F4HTB/uSDX-mOnO-PA/pictures/IMG_20220408_203908.jpg

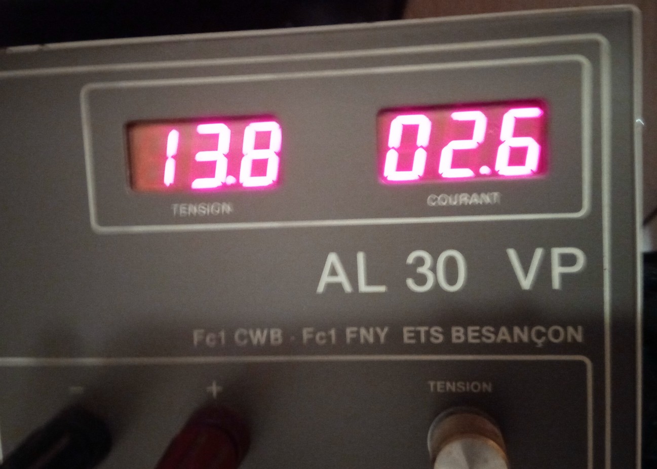
pictures/IMG_20220408_203908.jpg
