F4HTB/uSDX-mOnO-PA/Simulation/usdx_mOnO_PA_IRF530.asc

C1: cap; 10n
C2: cap; 100p
C3: cap; 200p
C4: cap; 100p
C5: cap; 12p
C6: cap; 33p
C7: cap; 10n
C8: cap; 1n
C9: cap; 100µ
C10: cap; 10n
L1: ind2; 5.76µ
L2: ind2; 13µ
L3: ind; 320n
L4: ind; 320n
L5: ind; 10µ
M1: nmos; IRF530
R1: res; 0.25
R2: res; 50
V1: voltage; SINE(3.96 4 28000000)
V2: voltage; 13.8; Rser=1
Named nets: 0
K1 L1 L2 1
.tran 500u
